davidgyongyosi/zmk-config/PCB/totem_0-3/TOTEM3D/xiao-ble-tht.step

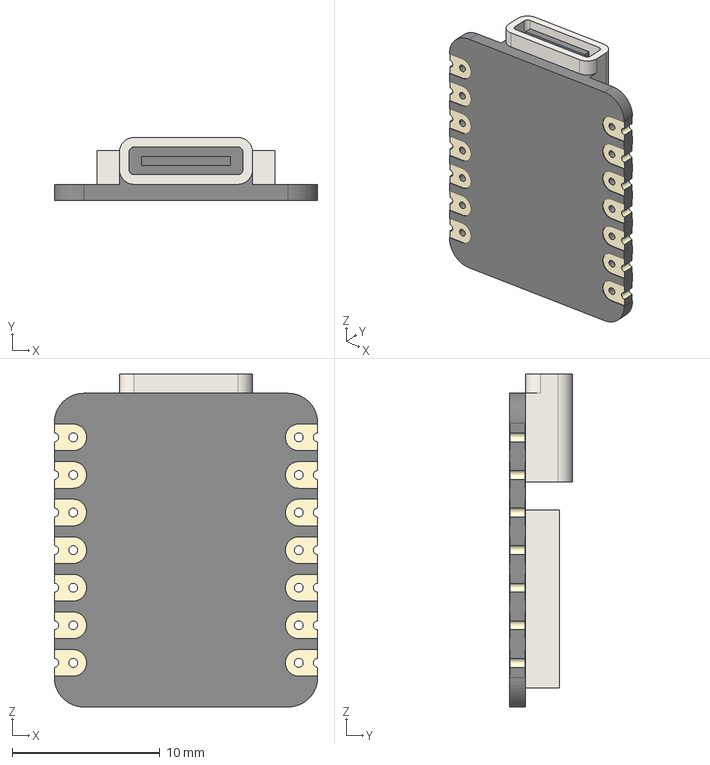
[picture p13: CAD file, 2025-03-07, last stored version]
PCB/totem_0-3/TOTEM3D/xiao-ble-tht.step
17.8 x 4.27 x 22.5 mm
