davidgyongyosi/zmk-config/PCB/totem_0-3/TOTEM3D/MSK12C02.STEP

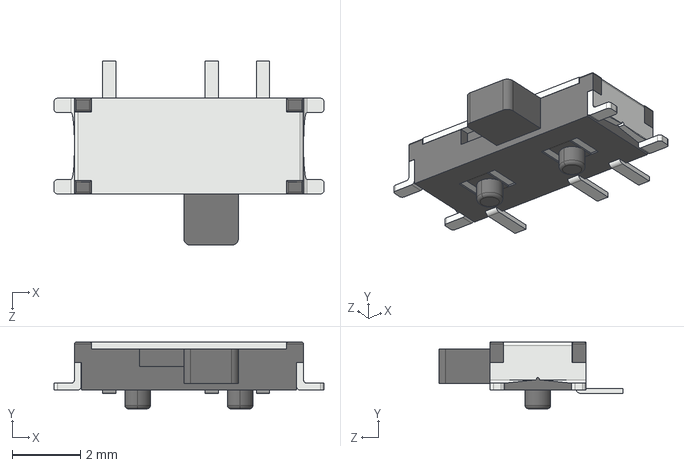
[picture p14: CAD file, 2025-03-07, last stored version]
PCB/totem_0-3/TOTEM3D/MSK12C02.STEP
7.90 x 1.95 x 5.39 mm
