davidgyongyosi/zmk-config/PCB/totem_0-3/TOTEM3D/Kailh_socket_PG1350_optional.STEP

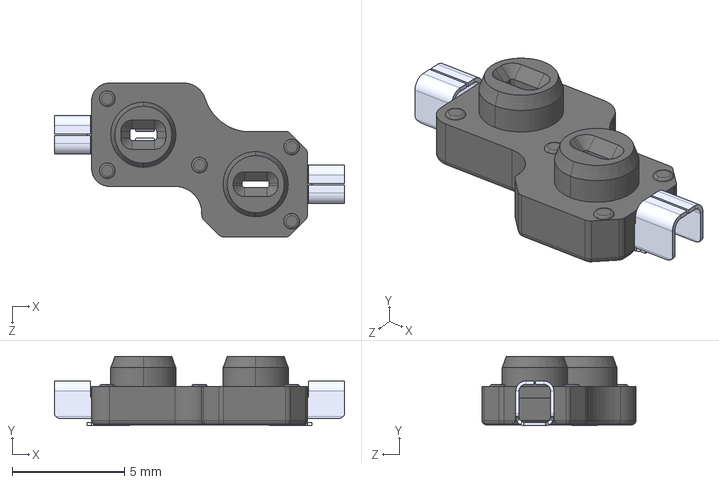
[picture p15: CAD file, 2025-03-07, last stored version]
PCB/totem_0-3/TOTEM3D/Kailh_socket_PG1350_optional.STEP
12.9 x 3.09 x 6.85 mm
pin x 2
socket
